DByte308/mi50-repaste/images/20260827_195303.jpg

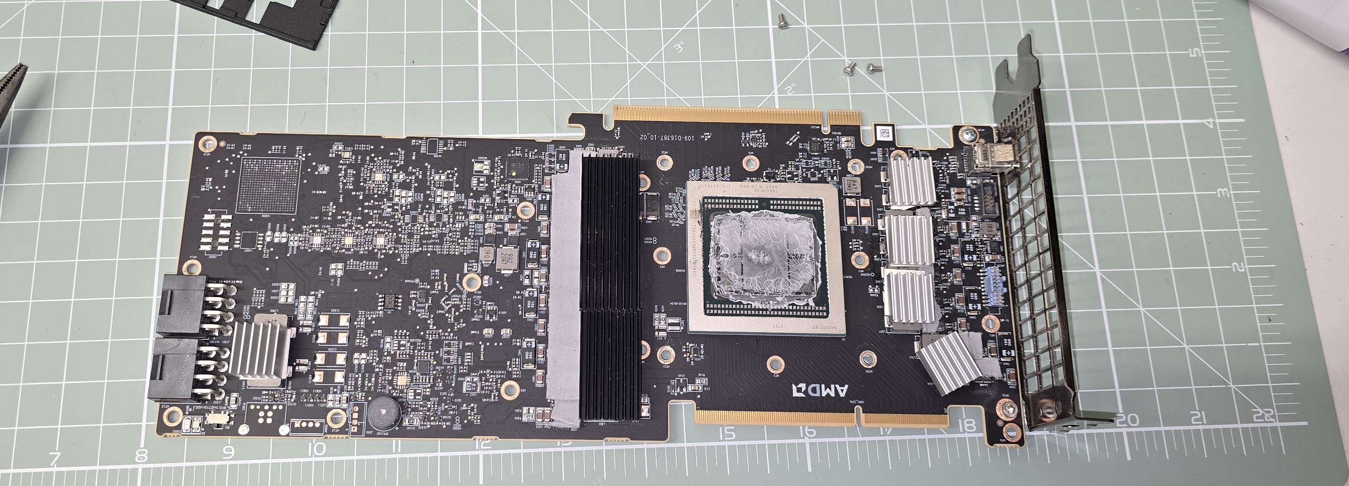
images/20260827_195303.jpg
